fedeboco/rfid-player/bins/config.h

#ifndef CONFIGH
#define CONFIGH

#include "Arduino.h"

#define ID_SIZE 11

class Config {
    private:
    int configButton;

    public:
    Config(int);
    bool readButton();
    void writeEEPROM(String, int);
    String readEEPROM(int);
    void writeFoldersEEPROM(int);
    int readFoldersEEPROM();
};

#endif
