fedeboco/rfid-player/bins/card.h

#ifndef CARDH
#define CARDH

#include <SPI.h>
#include <MFRC522.h>

class Card {
    private:
    MFRC522 cardReader;
    bool newCard = false;
    String card = "";

    public:
    Card(int, int);
    bool processCard();
    void init();
    String getCard();
    bool isNewCard();
    String getIDfromReader();
    bool updatesAvailable();

};

#endif
